easytarget/PrintPy2040/Python/Tools/logRRF/config.py

'''
    if neede  edit the serial device path and baud rate here, etc.
'''

class config():
    '''
        Serial Device Config:
        devices:  (list, strings) devices to try when connecting
                   - a list because under linux the /dev/ttyACM* and /dev/ttyUSB*
                     devices can wander between 0 and 1 when the duet reboots.
        baud:     (int) Serial baud rate; should match the setting used in the config.g
                  -  `M575` command used to enable the serial or usb port.
        quiet:    (bool) suppress info messages
    '''
    devices = ['/dev/ttyACM0','/dev/ttyACM1']
    baud = 57600
    quiet = False

    '''
        Timing and timeout config:
        updateTime:     (int, ms)  Basic time between update cycles
        requestTimeout: (int, ms)  maximum time to wait for response after sending request
                        - can be much longer than the serial blocking timeout above
        rebootDelay:    (int) Countdown in seconds when auto-restarting/rebooting
    '''
    updateTime = 1000
    requestTimeout = updateTime*0.66
    rebootDelay = 8

    '''
        Logging Config:
        - Replace "None" with "'filename.log'" to enable.
        rawLog:     An unprocessed raw log of all incoming serial data
        outputLog:  Log file for output module
                    - The example TXT output class will mirror it's output there
    '''
    rawLog = None
    outputLog = None
